nickbild/vectron_64/img/20190324_202425.jpg

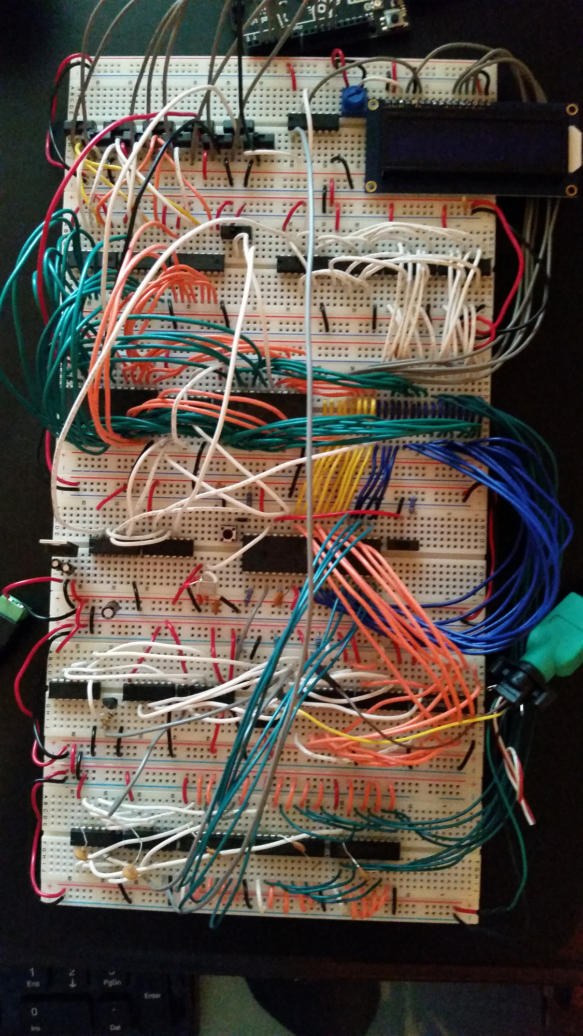
img/20190324_202425.jpg
